cinepost/msxxx/refs/oled_128_64/211014544-49f778af-5a19-4774-9d8c-9f28628b043a.png

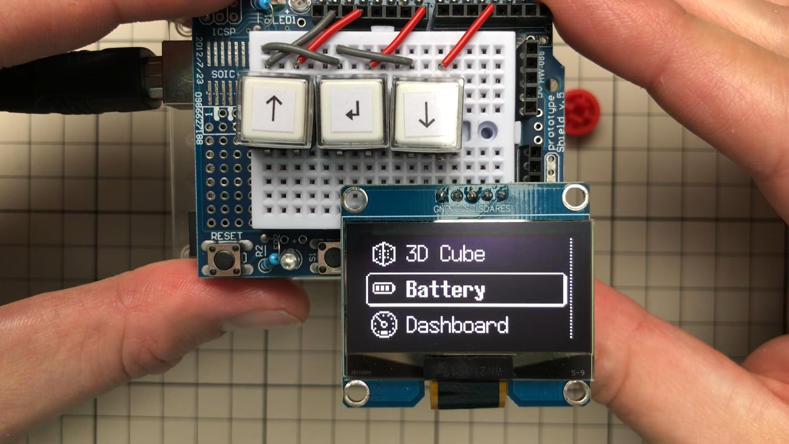
refs/oled_128_64/211014544-49f778af-5a19-4774-9d8c-9f28628b043a.png
